BaltasarParreira/SmallOLED-PCMonitor/src/web/web.h

/*
 * SmallOLED-PCMonitor - Web Server Module
 *
 * Web server handlers for configuration interface.
 */

#ifndef WEB_H
#define WEB_H

#include "../config/config.h"
#include <Update.h>
#include <WebServer.h>


#include "../config/settings.h"

// Global web server object
extern WebServer server;

// ========== Web Server Functions ==========

// Initialize web server with all routes
void setupWebServer();

// Web handlers
void handleRoot();
void handlePortalCss();
void handlePortalJs();
void handleSave();
void handleReset();
void handleMetricsAPI();
void handleDeviceInfo();
void handleRename();
void handleExportConfig();
void handleImportConfig();
void handleNtpTest();

// Runtime control API (display power, mode, brightness, clock style, reboot)
void handleStatus();
void handleDisplayOn();
void handleDisplayOff();
void handleSetBrightness();
#if LED_PWM_ENABLED
void handleLedOn();
void handleLedOff();
void handleLedBrightness();
#endif
void handleModeClock();
void handleModeAuto();
void handleModeViz();
void handleSetVizStyle();
#if VIZ_DEBUG_FB
void handleDebugFramebuffer();
#endif
void handleSetClockStyle();
void handleReboot();

#endif // WEB_H
